kdizon/2P-OPM/CAD/Custom Parts Linked With Drawings/ResGalvoMount_base_plate.stp

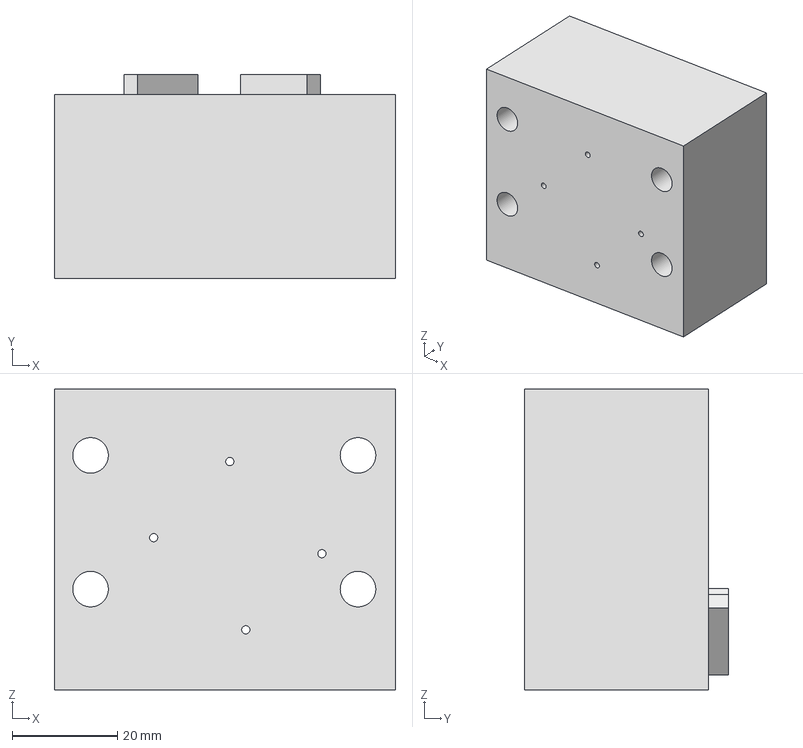
[picture p15: CAD file, 2025-10-08]
CAD/Custom Parts Linked With Drawings/ResGalvoMount_base_plate.stp
64.8 x 38.7 x 57.1 mm
