kdizon/2P-OPM/CAD/Imported Components/Coherent/Sapphire LP Heatsink with dowel pins.STEP

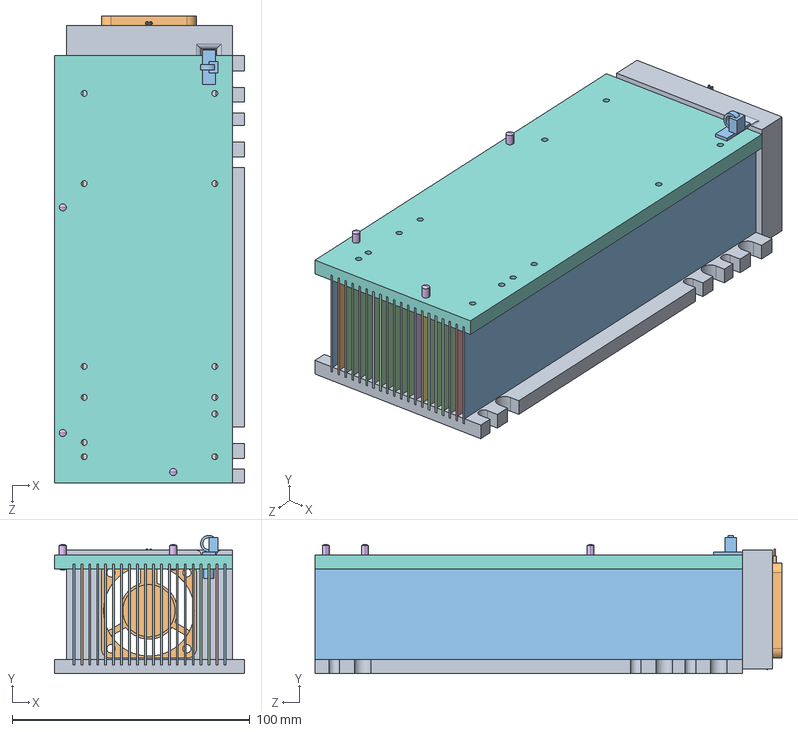
[picture p16: CAD file, 2025-10-09]
CAD/Imported Components/Coherent/Sapphire LP Heatsink with dowel pins.STEP
80.0 x 58.2 x 196.5 mm
