kdizon/2P-OPM/CAD/Imported Components/Edmund/EO_85678.step

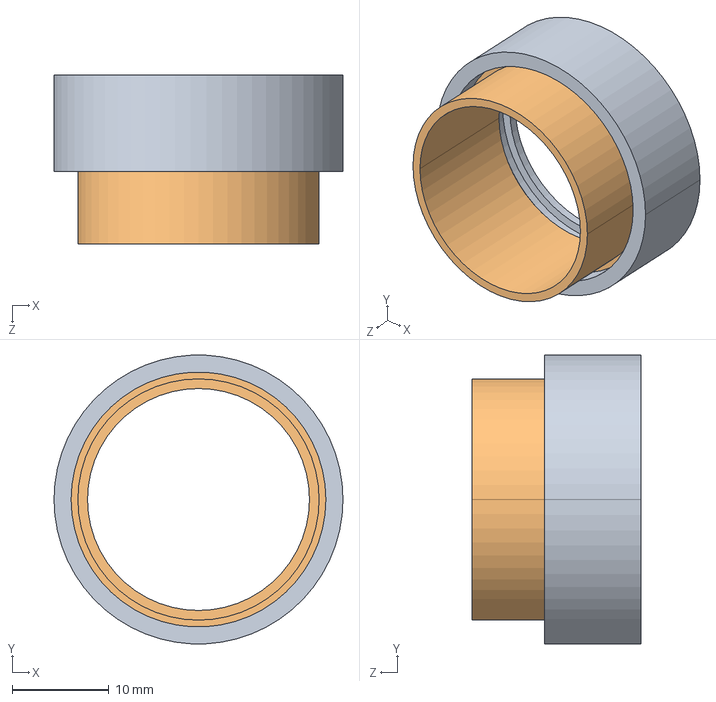
[picture p17: CAD file, 2025-10-09]
CAD/Imported Components/Edmund/EO_85678.step
30.0 x 29.9 x 17.5 mm
