kdizon/2P-OPM/CAD/Imported Components/Newport/Newport-SA2-11.stp

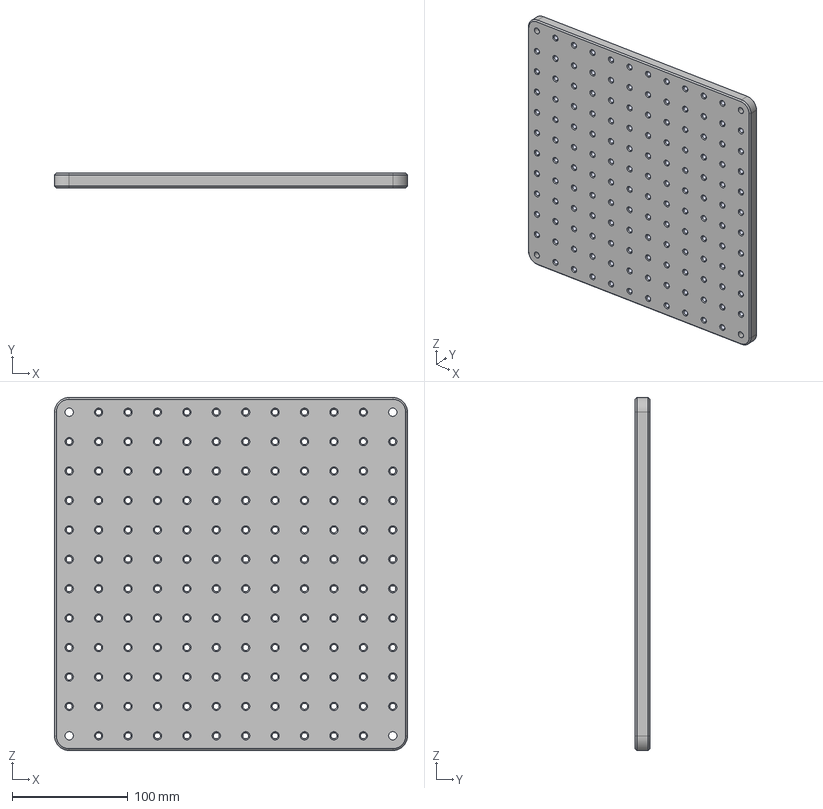
[picture p18: CAD file, 2025-10-09]
CAD/Imported Components/Newport/Newport-SA2-11.stp
304.8 x 12.7 x 304.8 mm
