kdizon/2P-OPM/CAD/Imported Components/PI/P725_1_adapterW0,8.STEP

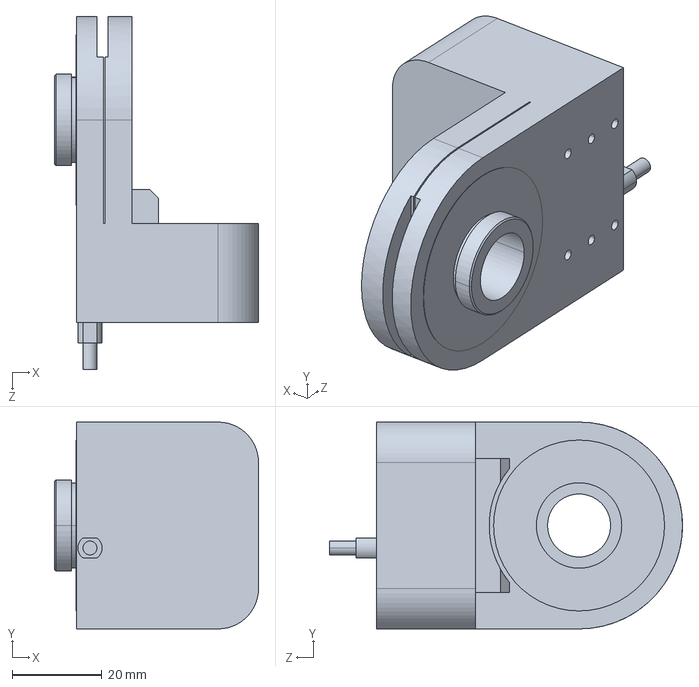
[picture p19: CAD file, 2025-10-09]
CAD/Imported Components/PI/P725_1_adapterW0,8.STEP
45.4 x 46.0 x 78.5 mm
