kdizon/2P-OPM/CAD/1P Laser Combiner/AA Optoelectronc AOTF-nc.sldprt

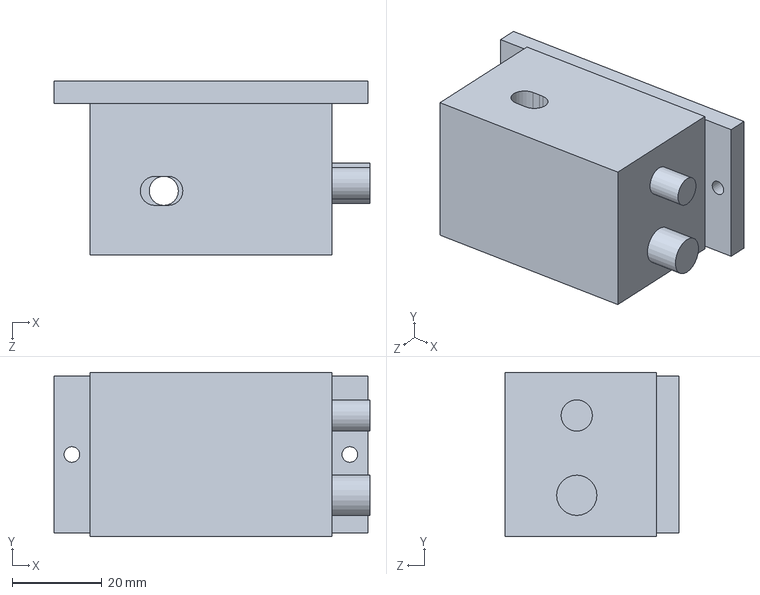
[picture p20: CAD file, 2025-10-08]
CAD/1P Laser Combiner/AA Optoelectronc AOTF-nc.sldprt
70.5 x 36.6 x 38.8 mm
