kdizon/2P-OPM/CAD/Custom Parts Linked With Drawings/xgalvo_to_base_clamp.stp

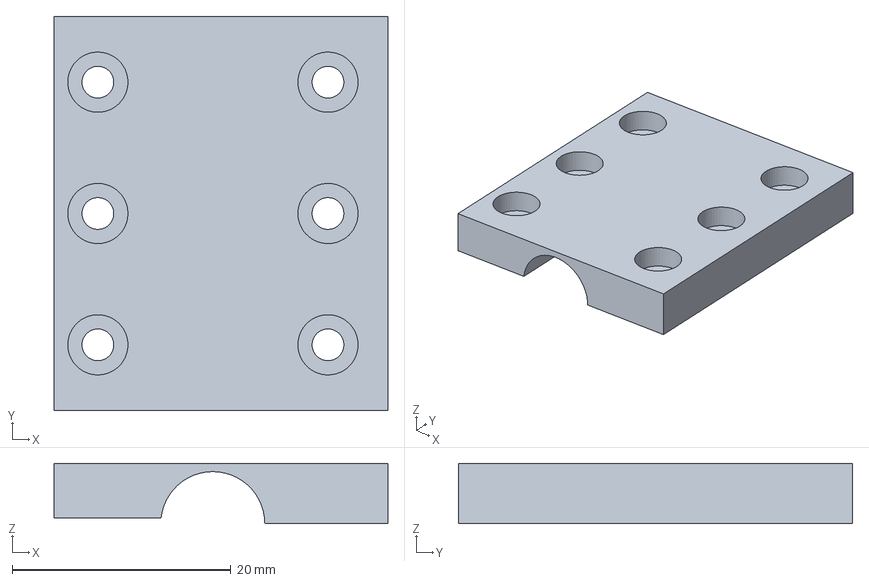
[picture p21: CAD file, 2025-10-08]
CAD/Custom Parts Linked With Drawings/xgalvo_to_base_clamp.stp
30.5 x 36.0 x 5.50 mm
