kdizon/2P-OPM/CAD/Imported Components/Edmund/EO_49287.stp

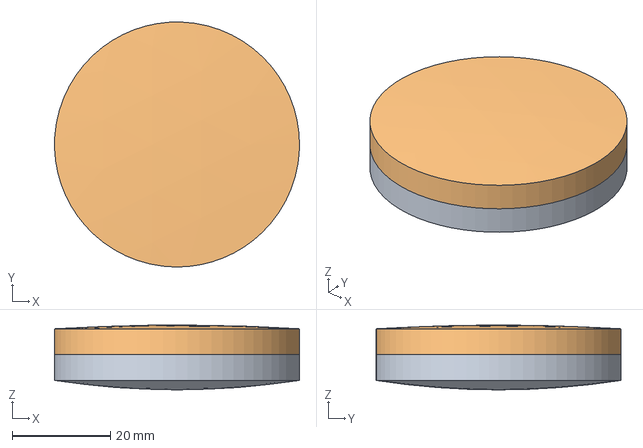
[picture p22: CAD file, 2025-10-09]
CAD/Imported Components/Edmund/EO_49287.stp
50.0 x 50.0 x 13.2 mm
