kdizon/2P-OPM/CAD/Imported Components/Newport/Newport-SA2-12.stp

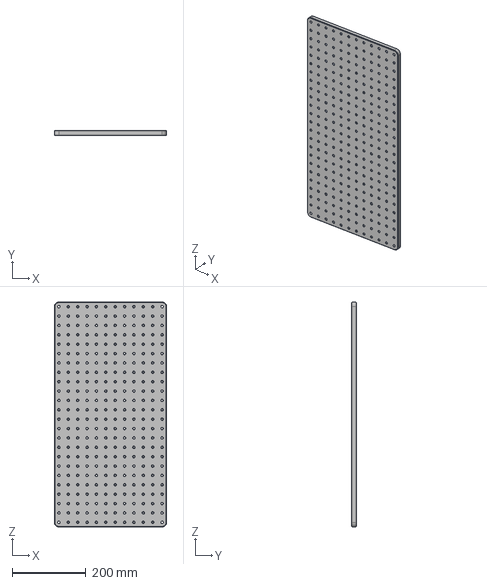
[picture p23: CAD file, 2025-10-09]
CAD/Imported Components/Newport/Newport-SA2-12.stp
304.8 x 12.7 x 609.6 mm
