kdizon/2P-OPM/CAD/Imported Components/PI/P-725.1CX+2CX.STEP

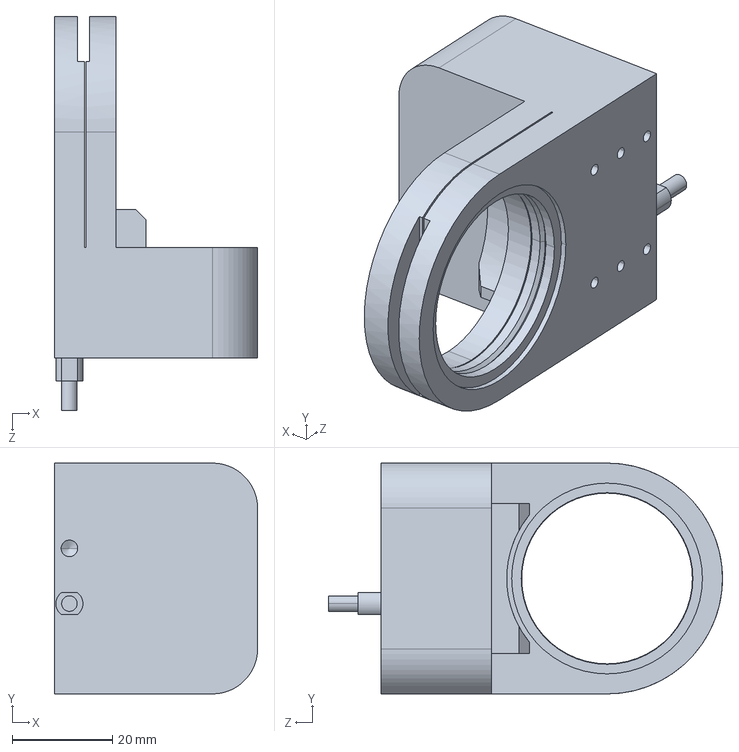
[picture p24: CAD file, 2025-10-09]
CAD/Imported Components/PI/P-725.1CX+2CX.STEP
40.5 x 46.0 x 78.5 mm
