kdizon/2P-OPM/CAD/1P Laser Combiner/Semrock LM01-503-25 LaserMUX dichroic beamsplitter.sldprt

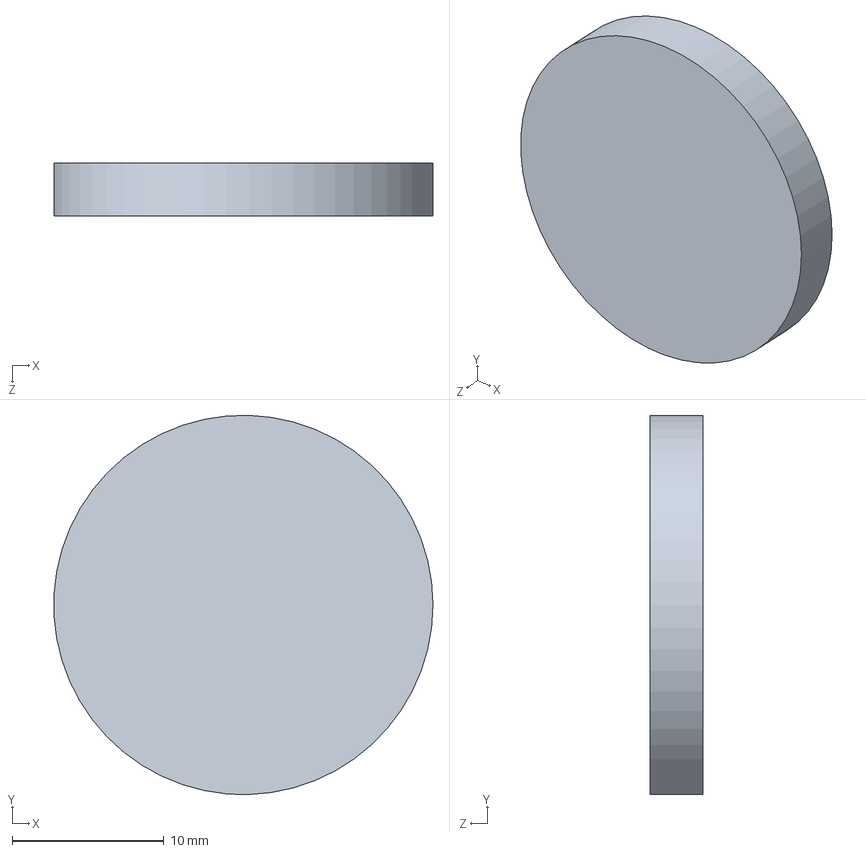
[picture p25: CAD file, 2025-10-08]
CAD/1P Laser Combiner/Semrock LM01-503-25 LaserMUX dichroic beamsplitter.sldprt
25.0 x 25.0 x 3.50 mm
