kdizon/2P-OPM/CAD/Custom Parts Linked With Drawings/ResGalvoMount_wobble.stp

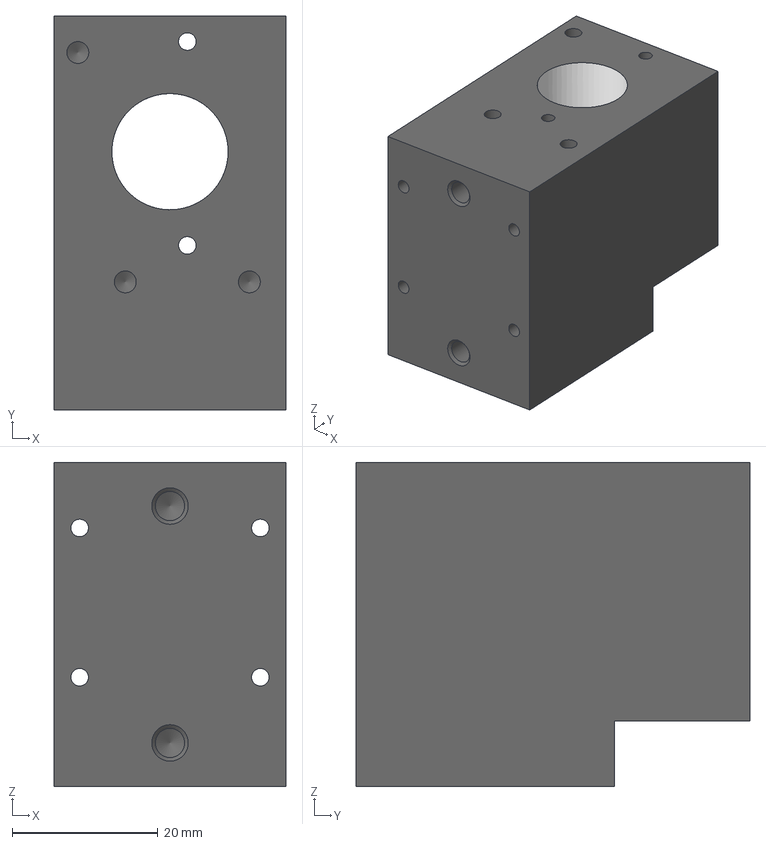
[picture p26: CAD file, 2025-10-08]
CAD/Custom Parts Linked With Drawings/ResGalvoMount_wobble.stp
31.8 x 54.0 x 44.5 mm
