kdizon/2P-OPM/CAD/Imported Components/Edmund/EO_85547.step

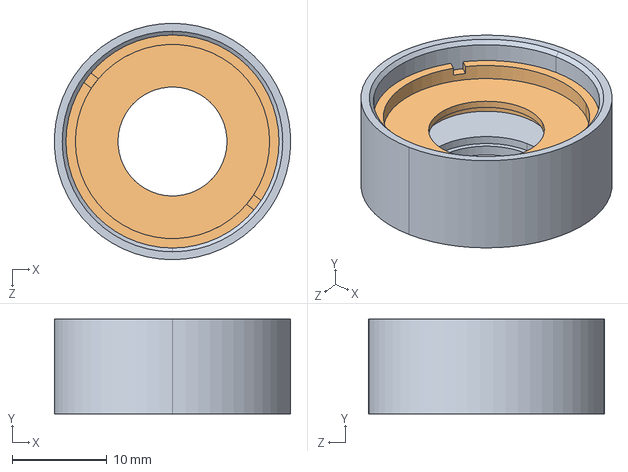
[picture p27: CAD file, 2025-10-09]
CAD/Imported Components/Edmund/EO_85547.step
24.9 x 10.0 x 25.0 mm
