kdizon/2P-OPM/CAD/Imported Components/Newport/Newport-RS4000-48-8.stp

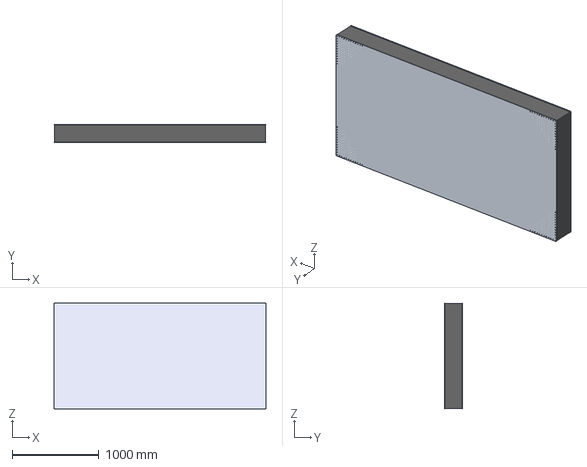
[picture p28: CAD file, 2025-10-09]
CAD/Imported Components/Newport/Newport-RS4000-48-8.stp
2438.4 x 203.2 x 1219.2 mm
