kdizon/2P-OPM/CAD/Imported Components/PI/P-725.2SL.STEP

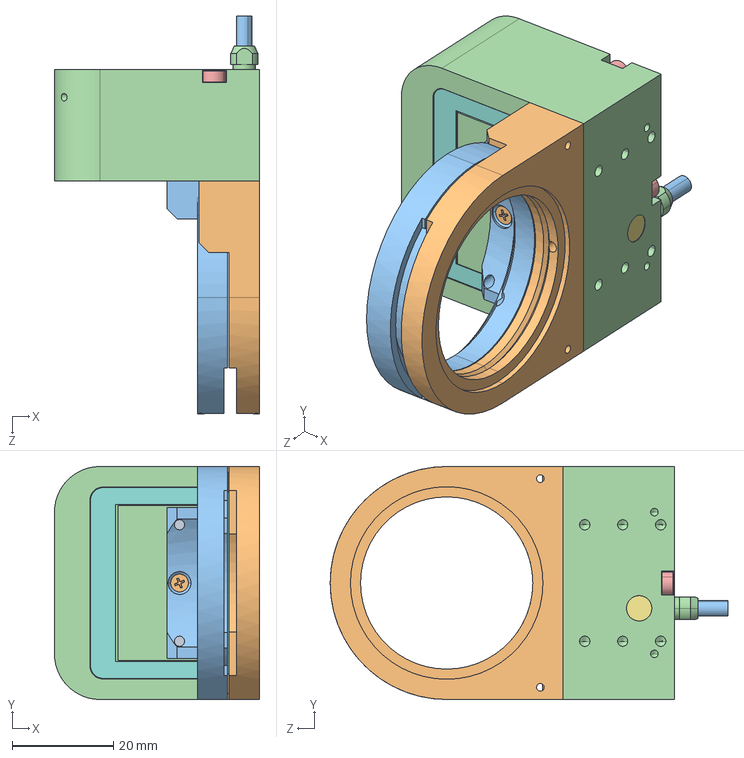
[picture p29: CAD file, 2025-10-09]
CAD/Imported Components/PI/P-725.2SL.STEP
40.5 x 46.0 x 78.5 mm
