kdizon/2P-OPM/CAD/1P Laser Combiner/EO_87371.step

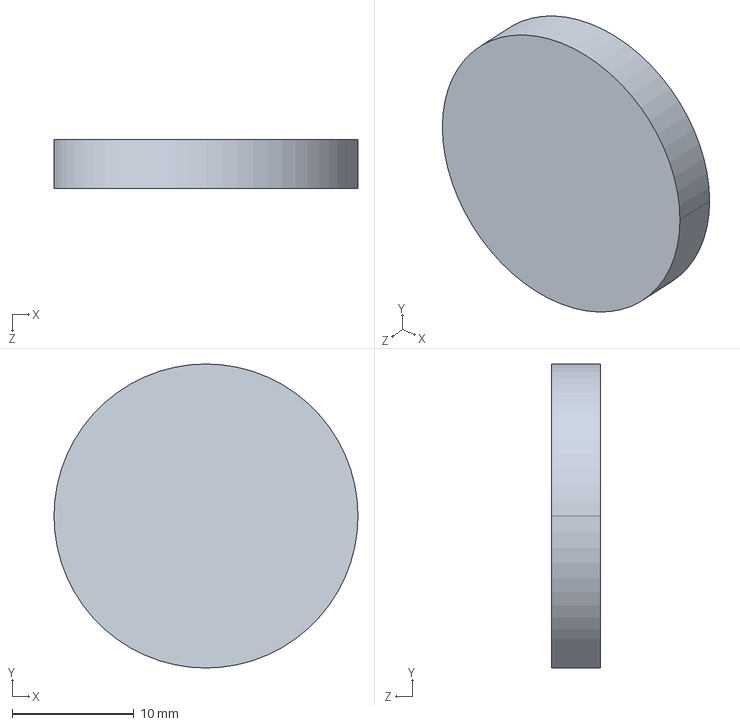
[picture p30: CAD file, 2025-10-08]
CAD/1P Laser Combiner/EO_87371.step
25.0 x 25.0 x 4.00 mm
