kdizon/2P-OPM/CAD/Custom Parts Linked With Drawings/xgalvo_to_newport_stage.stp

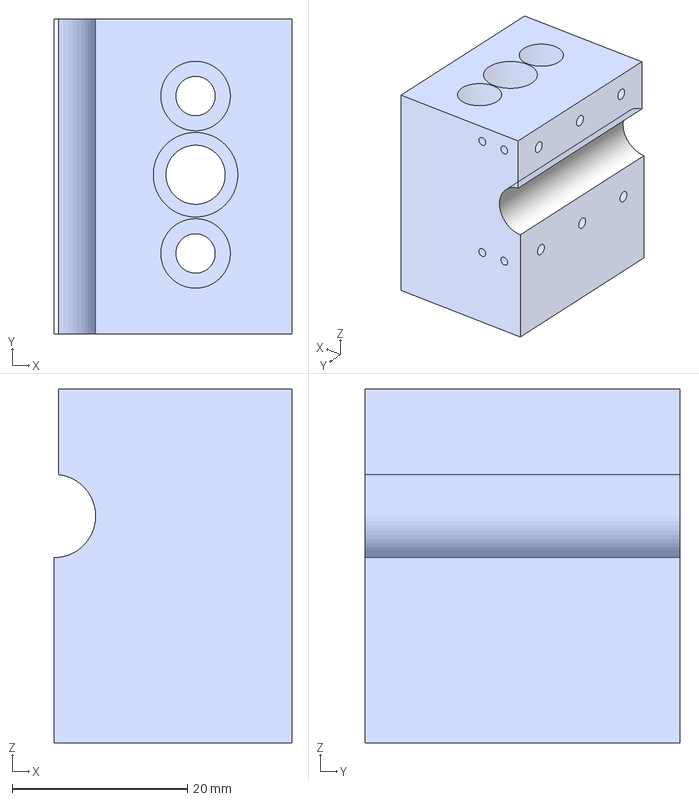
[picture p31: CAD file, 2025-10-08]
CAD/Custom Parts Linked With Drawings/xgalvo_to_newport_stage.stp
27.1 x 36.0 x 40.4 mm
