kdizon/2P-OPM/CAD/Imported Components/Edmund/EO_49304.stp

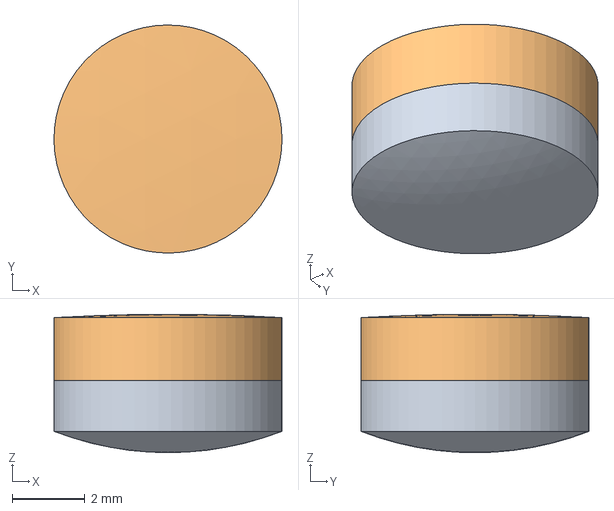
[picture p32: CAD file, 2025-10-09]
CAD/Imported Components/Edmund/EO_49304.stp
6.25 x 6.25 x 3.80 mm
