kdizon/2P-OPM/CAD/Imported Components/Newport/Newport-SM-13.stp

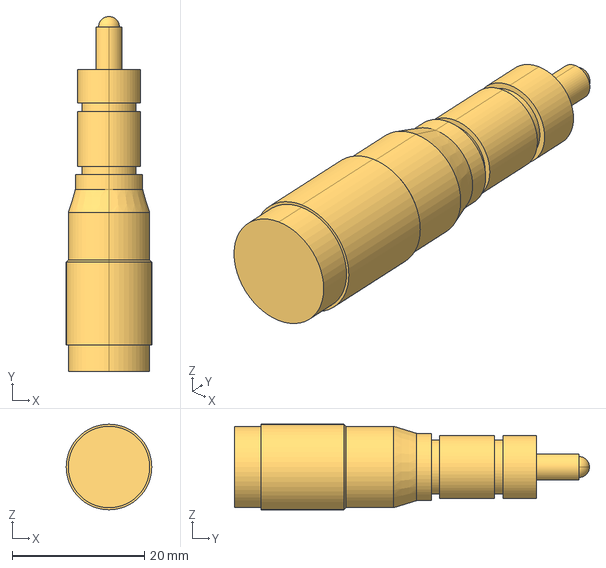
[picture p33: CAD file, 2025-10-09]
CAD/Imported Components/Newport/Newport-SM-13.stp
13.0 x 53.7 x 13.0 mm
