kdizon/2P-OPM/CAD/Custom Parts Linked With Drawings/20-1531-001_ResGalvoClamp.stp

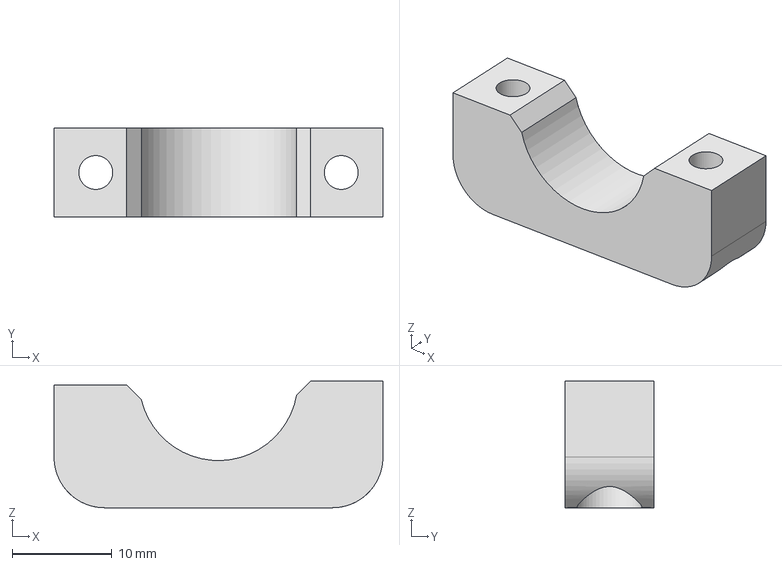
[picture p34: CAD file, 2025-10-08]
CAD/Custom Parts Linked With Drawings/20-1531-001_ResGalvoClamp.stp
33.0 x 8.89 x 12.7 mm
