kdizon/2P-OPM/CAD/Imported Components/Edmund/EO_49392.stp

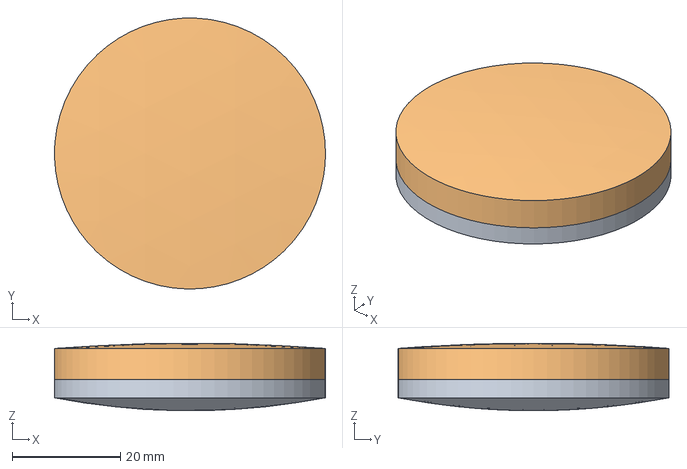
[picture p35: CAD file, 2025-10-09]
CAD/Imported Components/Edmund/EO_49392.stp
50.0 x 50.0 x 12.4 mm
