kdizon/2P-OPM/CAD/Imported Components/Newport/Newport-PRL-36.stp

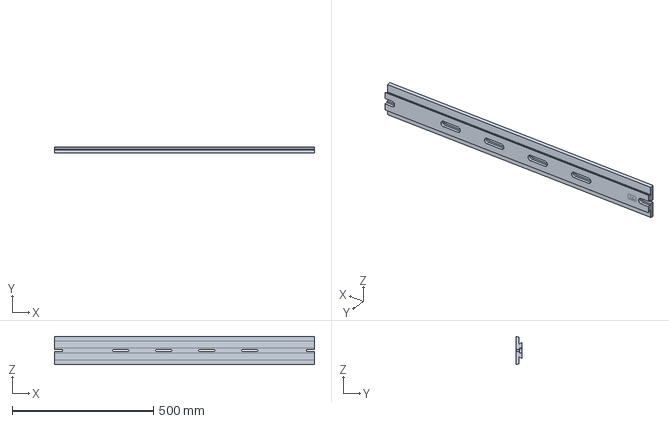
[picture p36: CAD file, 2025-10-09]
CAD/Imported Components/Newport/Newport-PRL-36.stp
921.5 x 21.1 x 99.3 mm
