kdizon/2P-OPM/CAD/Imported Components/Edmund/EO_right-angle-bracket_55378.step

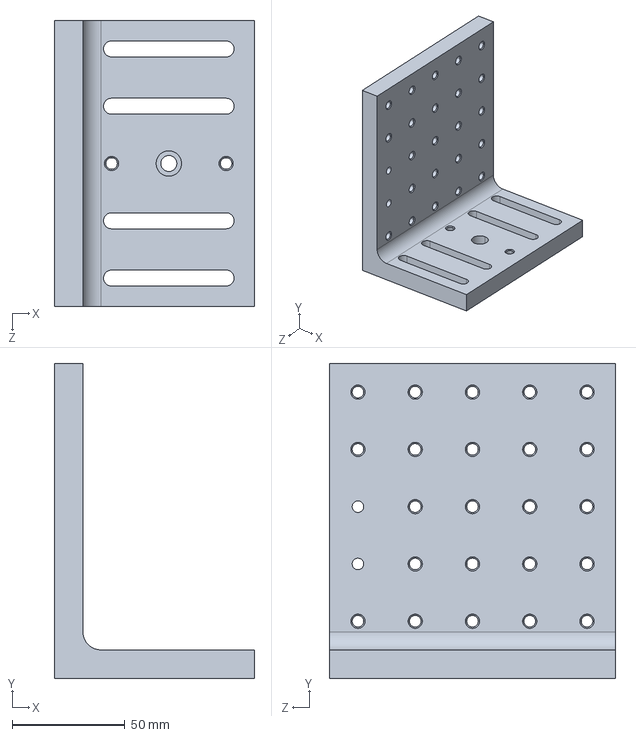
[picture p37: CAD file, 2025-10-09]
CAD/Imported Components/Edmund/EO_right-angle-bracket_55378.step
88.9 x 139.7 x 127.0 mm
