kdizon/2P-OPM/CAD/Imported Components/Newport/Newport-SM-25.stp

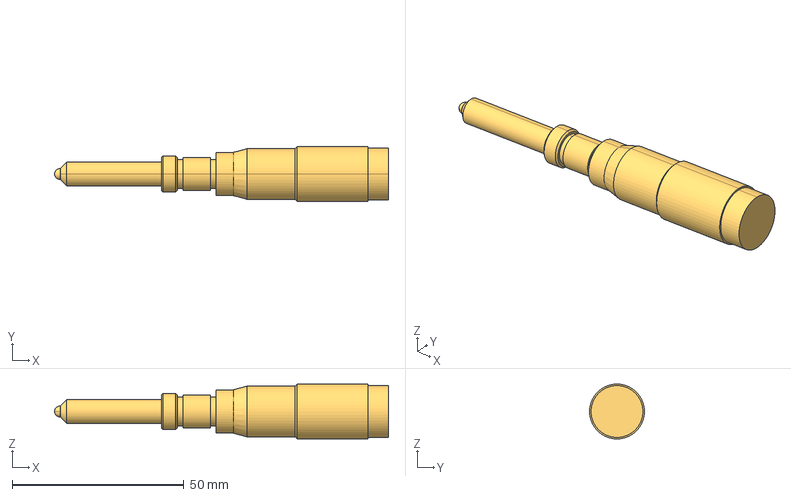
[picture p38: CAD file, 2025-10-09]
CAD/Imported Components/Newport/Newport-SM-25.stp
97.3 x 16.0 x 16.0 mm
