kdizon/2P-OPM/CAD/Imported Components/Edmund/EO_88196.STEP

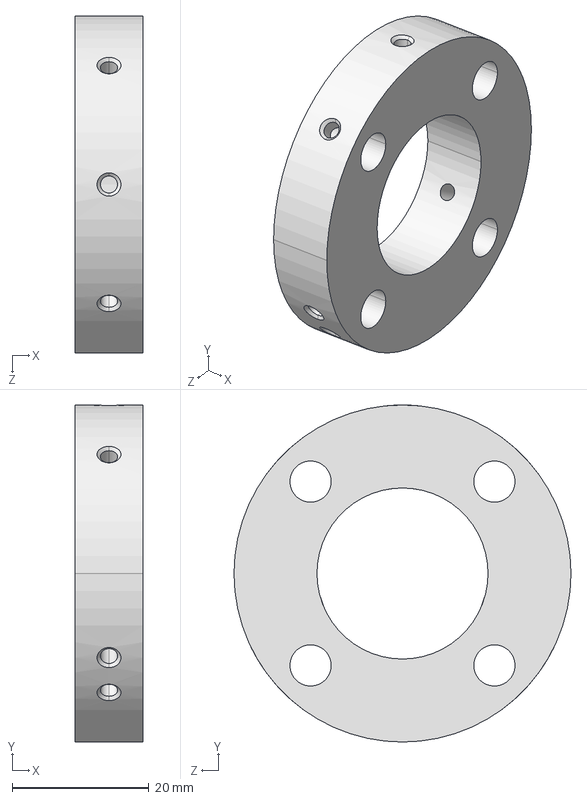
[picture p39: CAD file, 2025-10-09]
CAD/Imported Components/Edmund/EO_88196.STEP
10.0 x 49.2 x 49.2 mm
