kdizon/2P-OPM/CAD/Imported Components/Newport/Newport-TD-23.stp

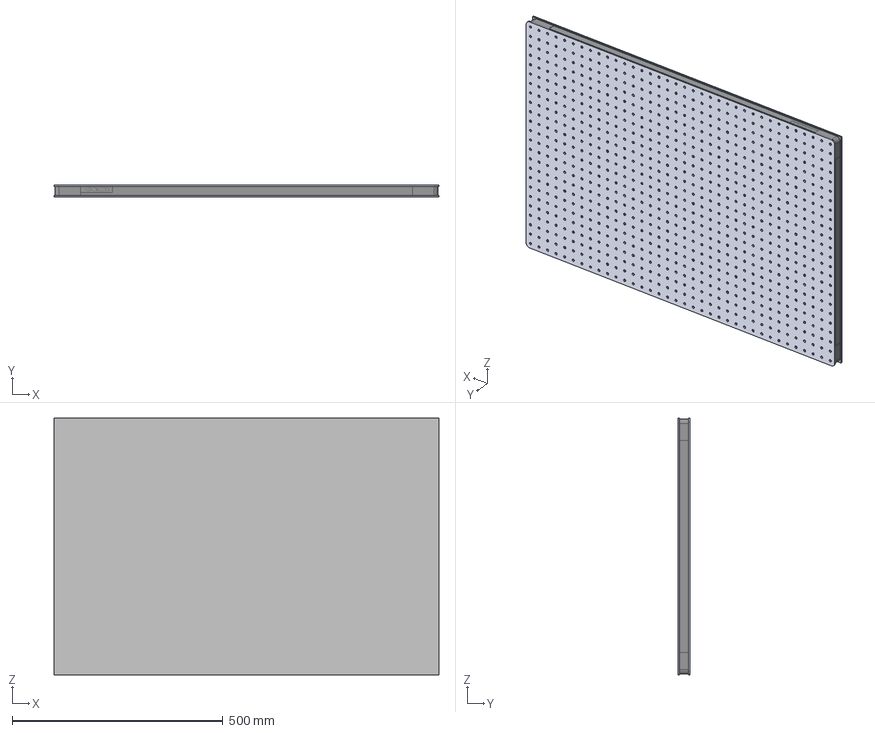
[picture p40: CAD file, 2025-10-09]
CAD/Imported Components/Newport/Newport-TD-23.stp
914.4 x 27.4 x 609.6 mm
