kdizon/2P-OPM/CAD/1P Laser Combiner/mirror translation stage adapter - 2P-OPM.stp

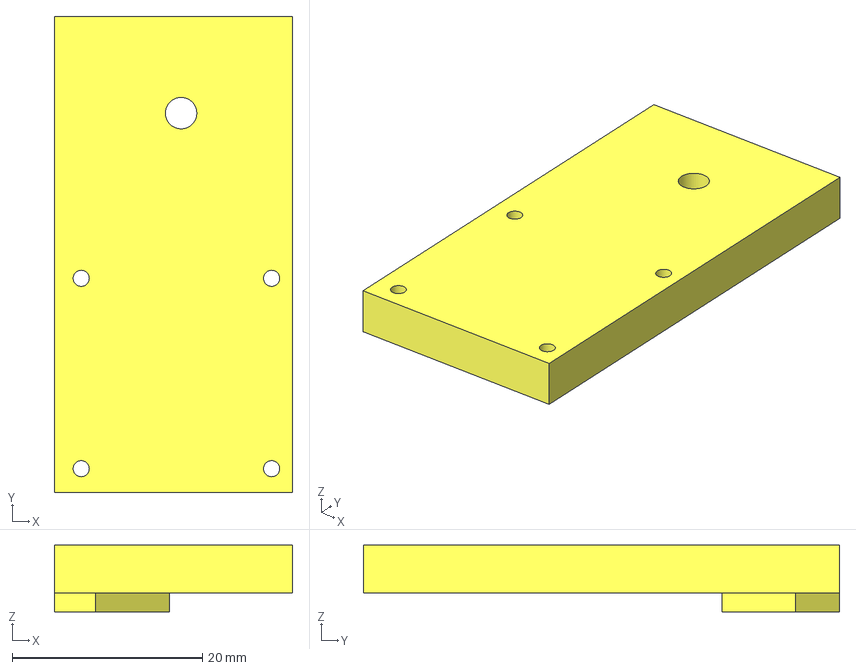
[picture p41: CAD file, 2025-10-08]
CAD/1P Laser Combiner/mirror translation stage adapter - 2P-OPM.stp
25.0 x 50.0 x 7.00 mm
