kdizon/2P-OPM/CAD/Imported Components/Edmund/EO_12.5mmDia_90mmFL_49332.stp

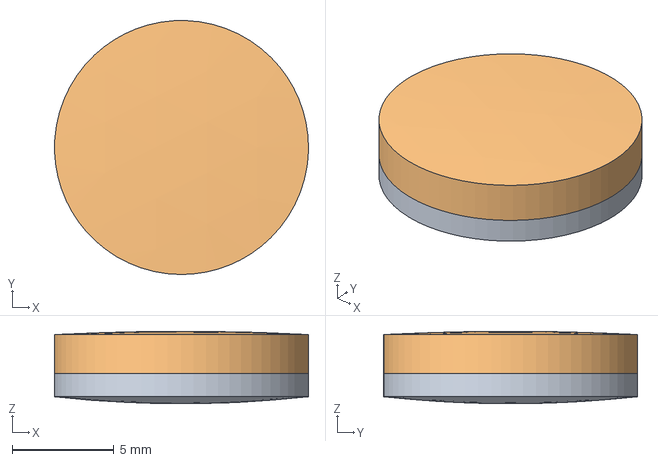
[picture p42: CAD file, 2025-10-09]
CAD/Imported Components/Edmund/EO_12.5mmDia_90mmFL_49332.stp
12.5 x 12.5 x 3.57 mm
