kdizon/2P-OPM/CAD/Imported Components/Newport/Newport-PRC-1.stp

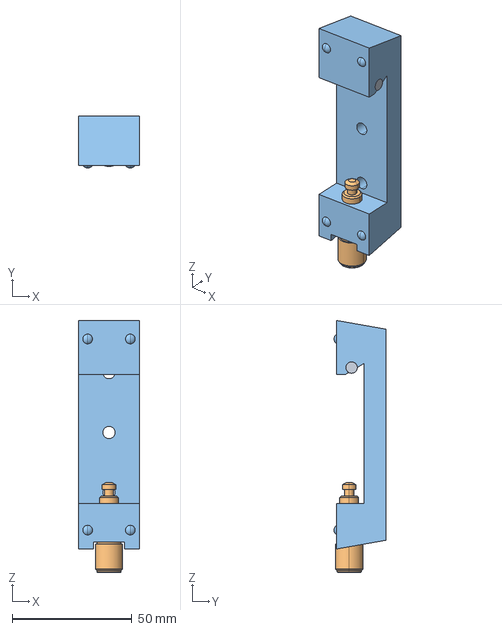
[picture p43: CAD file, 2025-10-09]
CAD/Imported Components/Newport/Newport-PRC-1.stp
25.4 x 21.7 x 105.2 mm
