kdizon/2P-OPM/CAD/1P Laser Combiner/baseblock for AOTF.stp

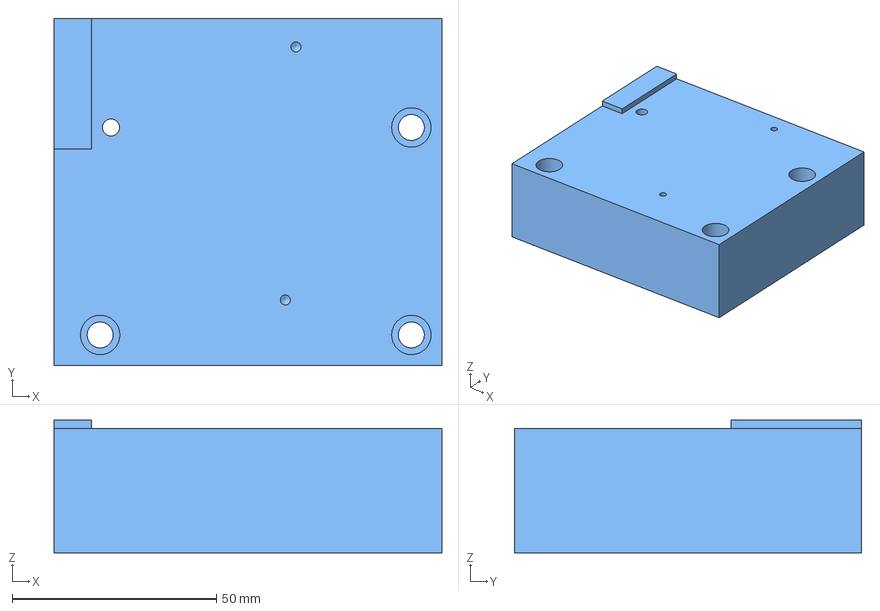
[picture p44: CAD file, 2025-10-08]
CAD/1P Laser Combiner/baseblock for AOTF.stp
95.0 x 85.0 x 32.5 mm
