kdizon/2P-OPM/CAD/Imported Components/Edmund/EO_84747.step

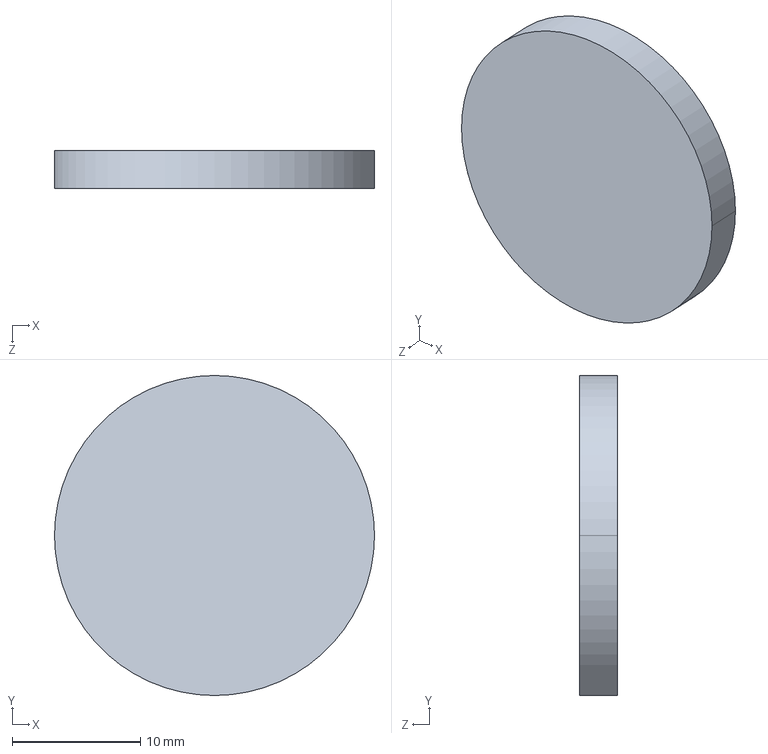
[picture p45: CAD file, 2025-10-09]
CAD/Imported Components/Edmund/EO_84747.step
25.0 x 25.0 x 3.00 mm
