kdizon/2P-OPM/CAD/Imported Components/Newport/Newport-B-2B.stp

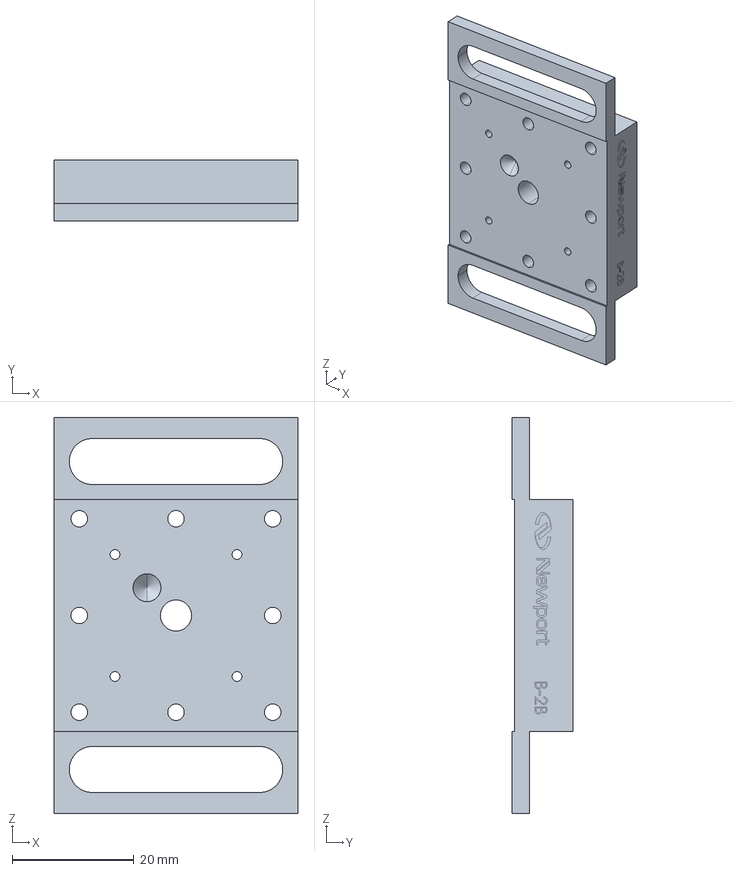
[picture p46: CAD file, 2025-10-09]
CAD/Imported Components/Newport/Newport-B-2B.stp
40.0 x 10.0 x 65.0 mm
