kdizon/2P-OPM/CAD/Imported Components/Edmund/EO_49288.stp

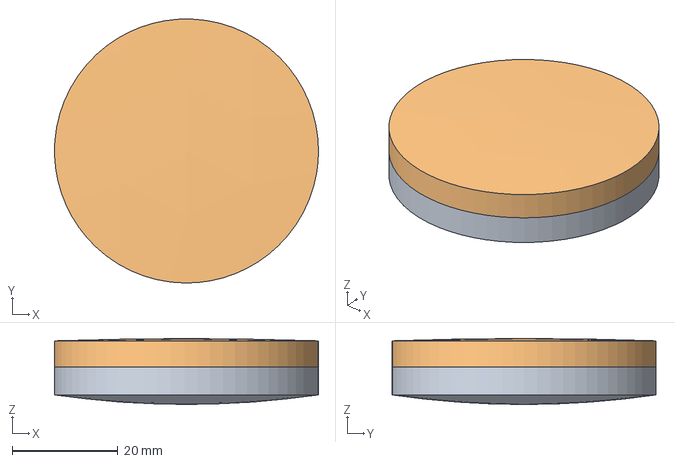
[picture p47: CAD file, 2025-10-09]
CAD/Imported Components/Edmund/EO_49288.stp
50.0 x 50.0 x 12.5 mm
