kdizon/2P-OPM/CAD/Imported Components/Newport/Newport-9884.stp

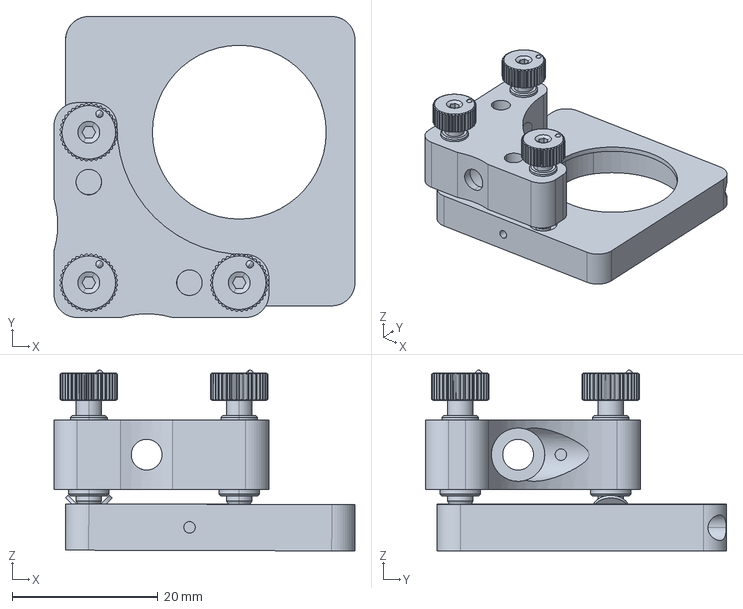
[picture p48: CAD file, 2025-10-09]
CAD/Imported Components/Newport/Newport-9884.stp
41.3 x 41.3 x 24.8 mm
