kdizon/2P-OPM/CAD/1P Laser Combiner/MRA10-E02 right angle prism dielectric coat.sldprt

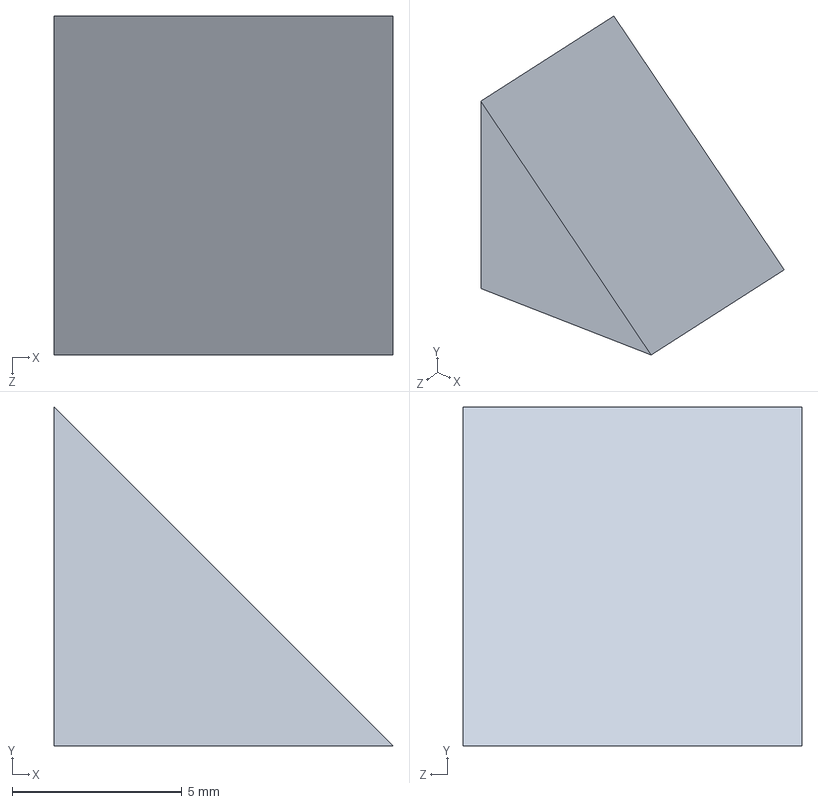
[picture p49: CAD file, 2025-10-08]
CAD/1P Laser Combiner/MRA10-E02 right angle prism dielectric coat.sldprt
10.0 x 10.0 x 10.0 mm
