kdizon/2P-OPM/CAD/Imported Components/Edmund/EO_49364.stp

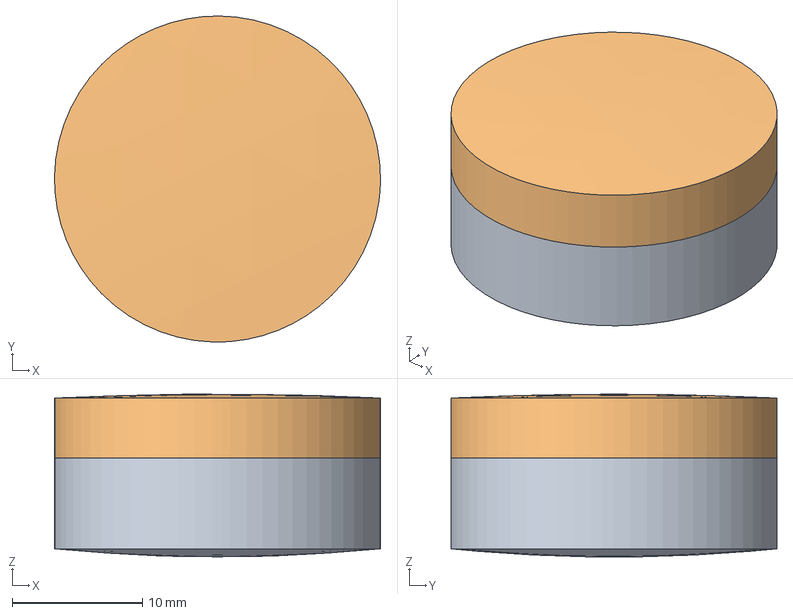
[picture p50: CAD file, 2025-10-09]
CAD/Imported Components/Edmund/EO_49364.stp
25.0 x 25.0 x 12.5 mm
