kdizon/2P-OPM/CAD/Imported Components/Newport/Newport-DS40-X.stp

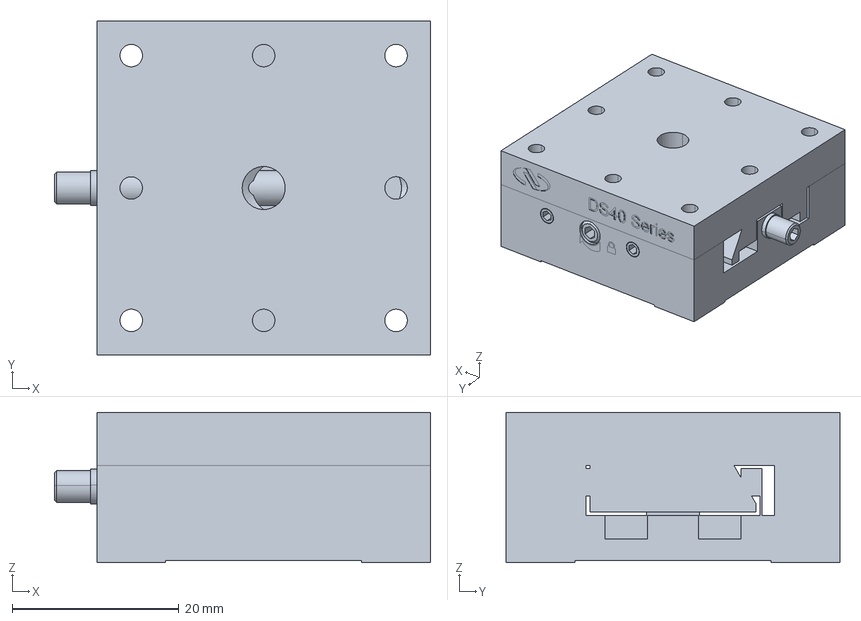
[picture p51: CAD file, 2025-10-09]
CAD/Imported Components/Newport/Newport-DS40-X.stp
45.1 x 40.0 x 18.0 mm
