kdizon/2P-OPM/CAD/Imported Components/Edmund/EO_85536.step

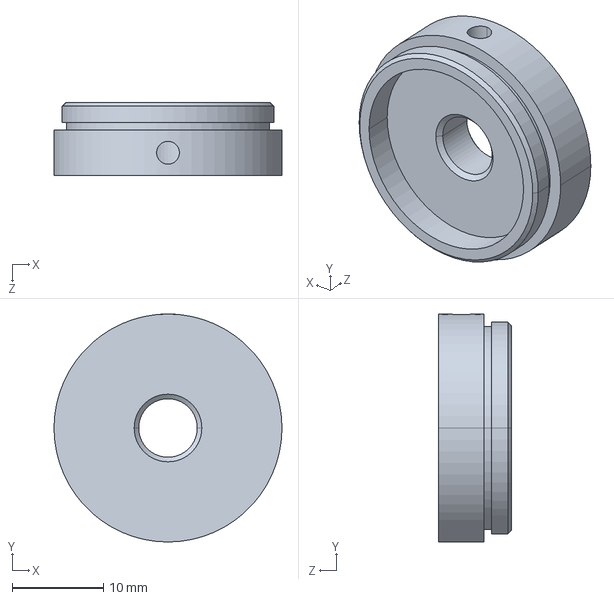
[picture p52: CAD file, 2025-10-09]
CAD/Imported Components/Edmund/EO_85536.step
25.0 x 25.0 x 8.00 mm
