kdizon/2P-OPM/CAD/Imported Components/Newport/Newport-PRL-12.stp

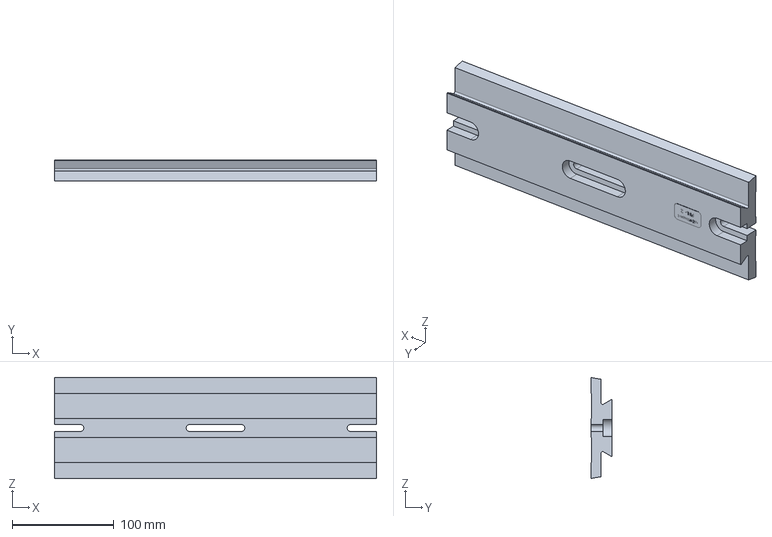
[picture p53: CAD file, 2025-10-09]
CAD/Imported Components/Newport/Newport-PRL-12.stp
316.5 x 21.1 x 99.3 mm
