kdizon/2P-OPM/CAD/Imported Components/Edmund/EO_47661.stp

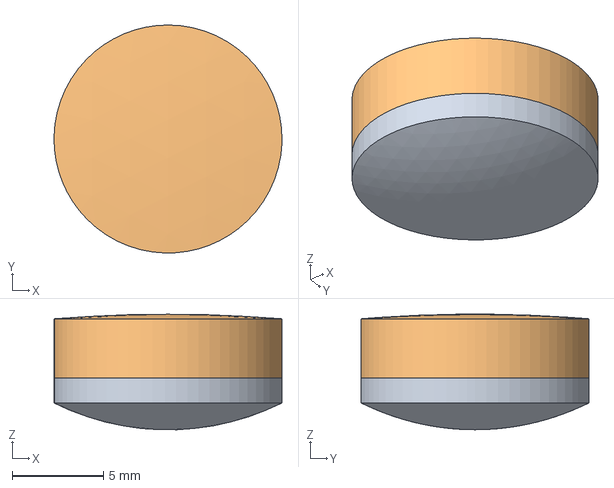
[picture p54: CAD file, 2025-10-09]
CAD/Imported Components/Edmund/EO_47661.stp
12.5 x 12.5 x 6.33 mm
