kdizon/2P-OPM/CAD/Imported Components/Newport/Newport-AJS100-1.stp

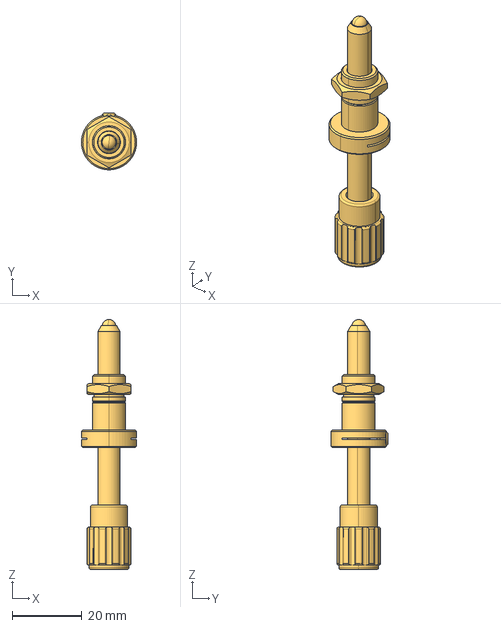
[picture p55: CAD file, 2025-10-09]
CAD/Imported Components/Newport/Newport-AJS100-1.stp
15.9 x 16.3 x 71.9 mm
