kdizon/2P-OPM/CAD/Imported Components/Edmund/EO_slotted_right-angle-bracket_58181.step

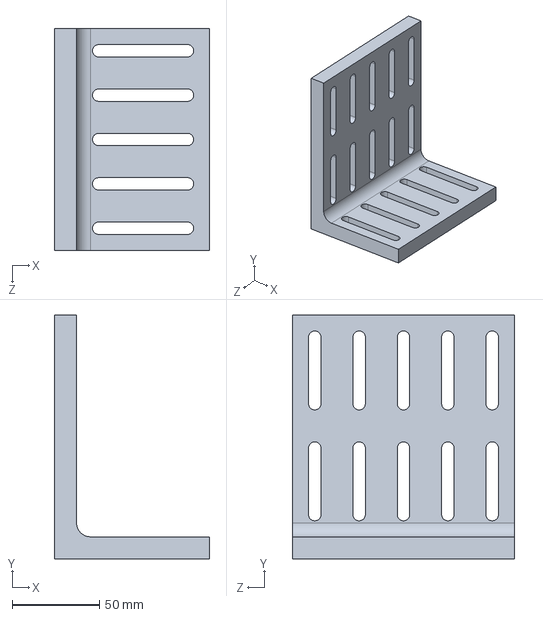
[picture p56: CAD file, 2025-10-09]
CAD/Imported Components/Edmund/EO_slotted_right-angle-bracket_58181.step
88.9 x 139.7 x 127.0 mm
