kdizon/2P-OPM/CAD/Imported Components/Newport/Newport-9066-XY.stp

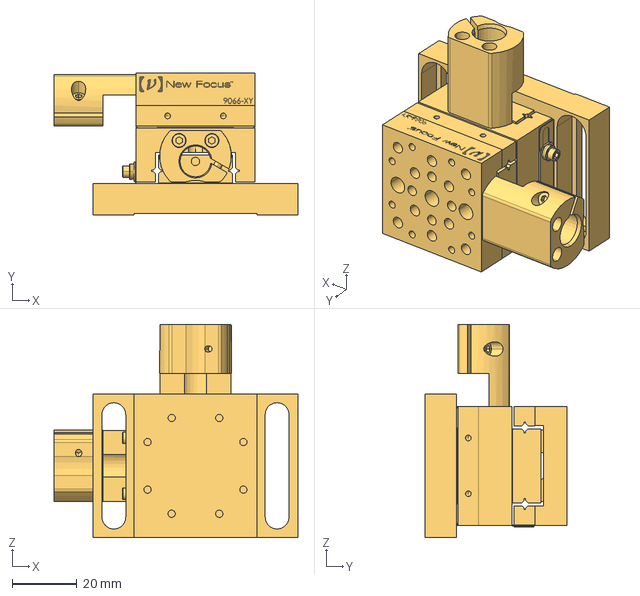
[picture p57: CAD file, 2025-10-09]
CAD/Imported Components/Newport/Newport-9066-XY.stp
75.6 x 44.1 x 66.0 mm
