kdizon/2P-OPM/CAD/Imported Components/Newport/Newport-433.stp

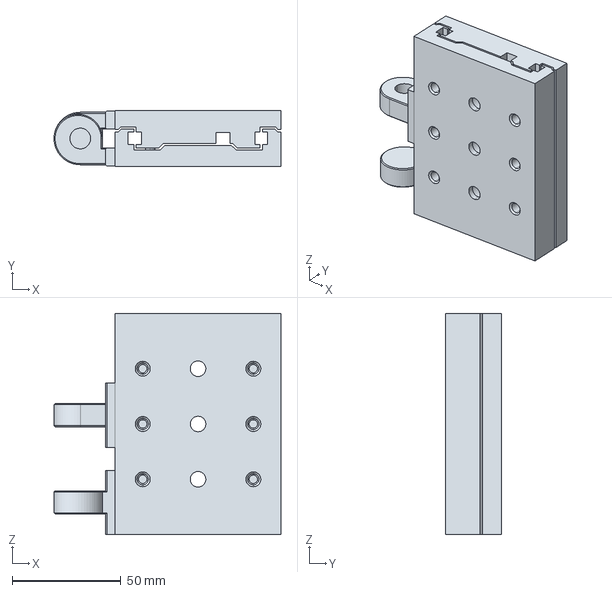
[picture p59: CAD file, 2025-10-09]
CAD/Imported Components/Newport/Newport-433.stp
104.3 x 25.7 x 101.6 mm
