kdizon/2P-OPM/CAD/Imported Components/Edmund/EO_49362.stp

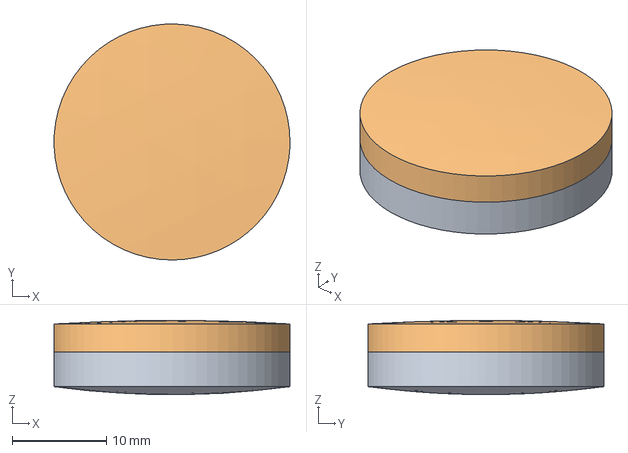
[picture p60: CAD file, 2025-10-09]
CAD/Imported Components/Edmund/EO_49362.stp
25.0 x 25.0 x 7.87 mm
