kdizon/2P-OPM/CAD/Imported Components/Newport/Newport-436.stp

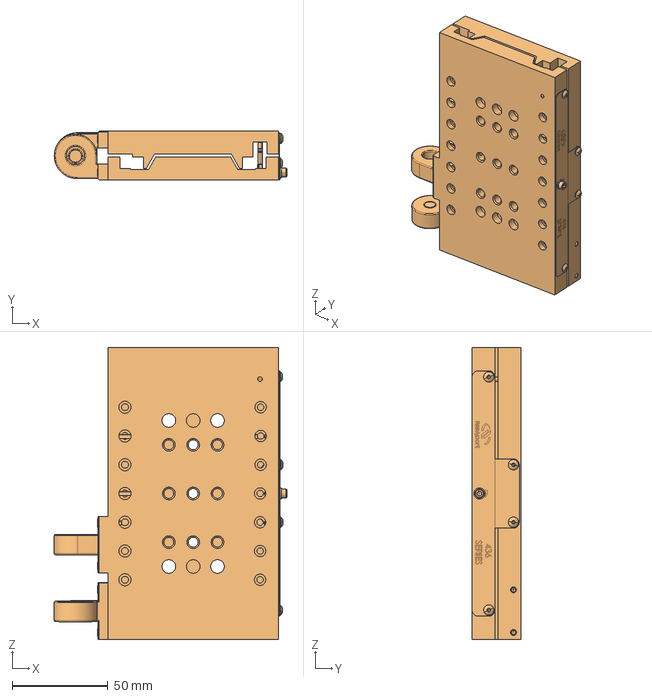
[picture p61: CAD file, 2025-10-09]
CAD/Imported Components/Newport/Newport-436.stp
121.4 x 25.5 x 152.4 mm
