kdizon/2P-OPM/CAD/Imported Components/Edmund/EO_small-slotted_right-angle-bracket_58180.step

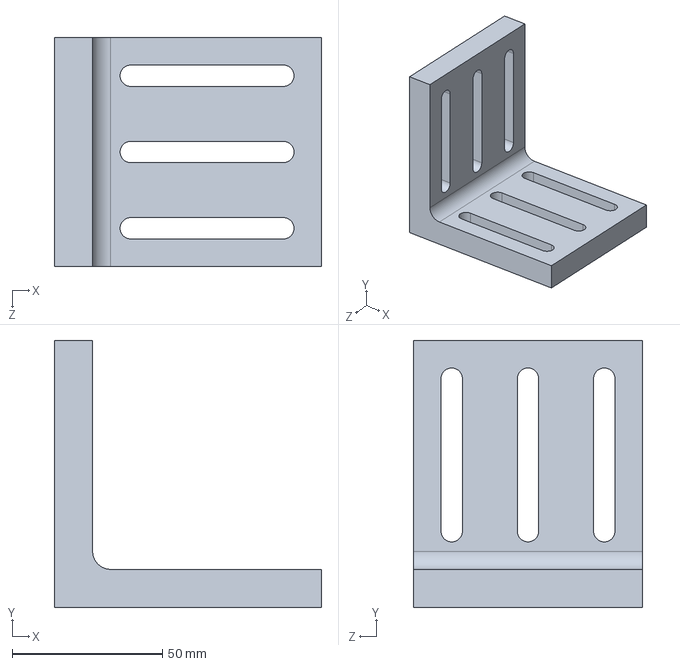
[picture p62: CAD file, 2025-10-09]
CAD/Imported Components/Edmund/EO_small-slotted_right-angle-bracket_58180.step
88.9 x 88.9 x 76.2 mm
