kdizon/2P-OPM/CAD/Imported Components/Newport/Newport-8892-K.stp

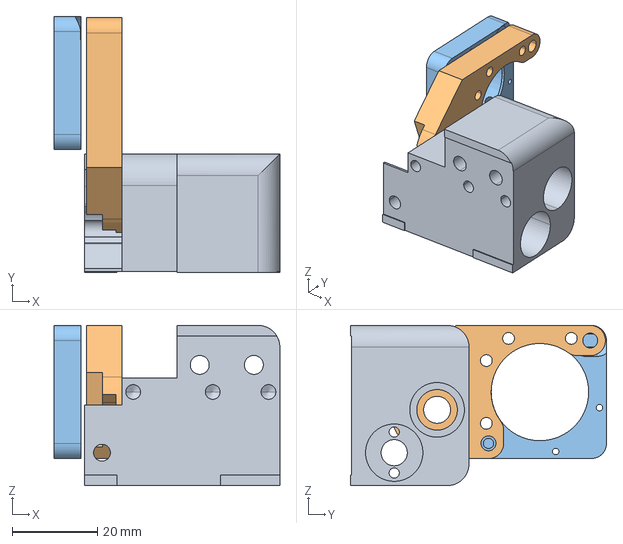
[picture p63: CAD file, 2025-10-09]
CAD/Imported Components/Newport/Newport-8892-K.stp
53.0 x 60.1 x 37.6 mm
