kdizon/2P-OPM/CAD/Imported Components/Edmund/EO_49947.stp

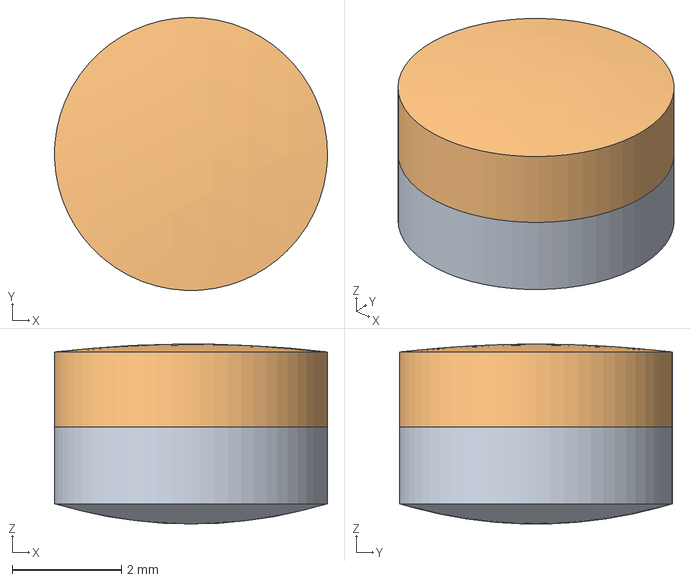
[picture p64: CAD file, 2025-10-09]
CAD/Imported Components/Edmund/EO_49947.stp
5.00 x 5.00 x 3.29 mm
