kdizon/2P-OPM/CAD/Imported Components/Newport/Newport-443.stp

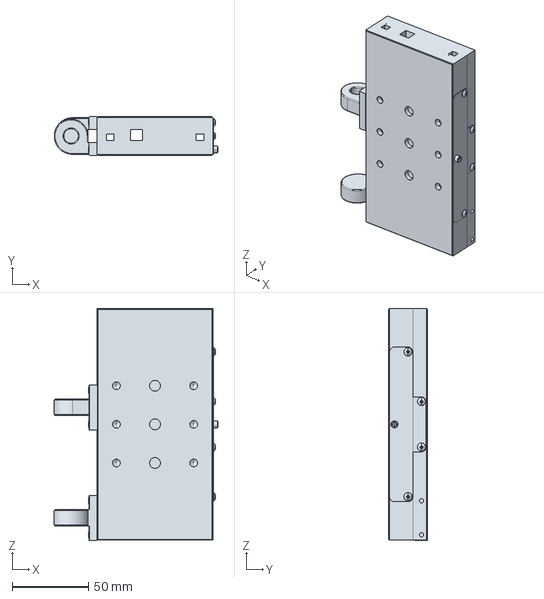
[picture p65: CAD file, 2025-10-09]
CAD/Imported Components/Newport/Newport-443.stp
107.5 x 25.4 x 152.6 mm
