kdizon/2P-OPM/CAD/Imported Components/Newport/Newport-9481.stp

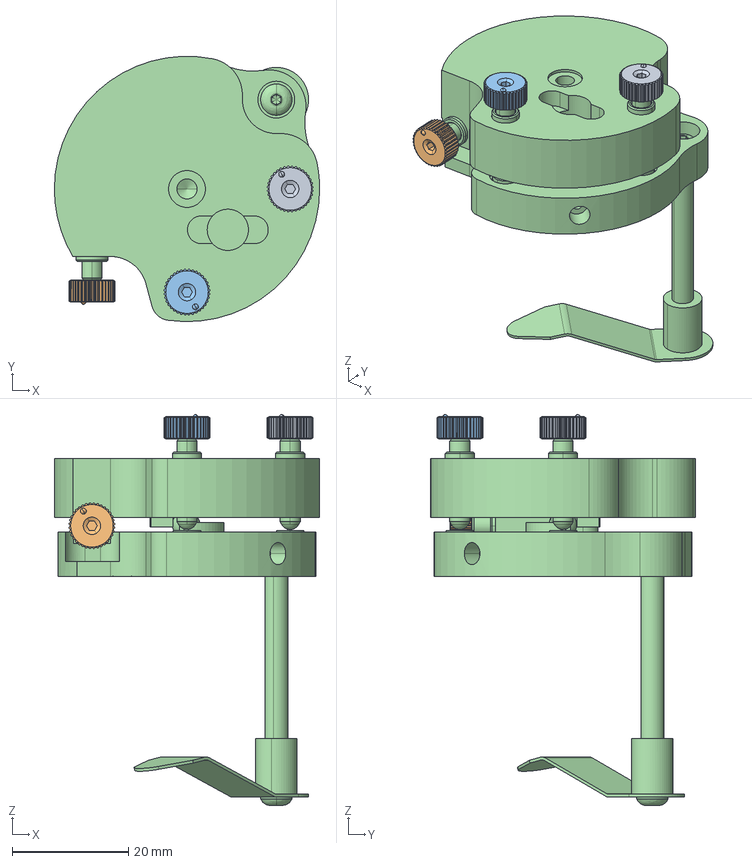
[picture p66: CAD file, 2025-10-09]
CAD/Imported Components/Newport/Newport-9481.stp
45.7 x 45.7 x 67.4 mm
