kdizon/2P-OPM/CAD/Imported Components/Newport/Newport-423.stp

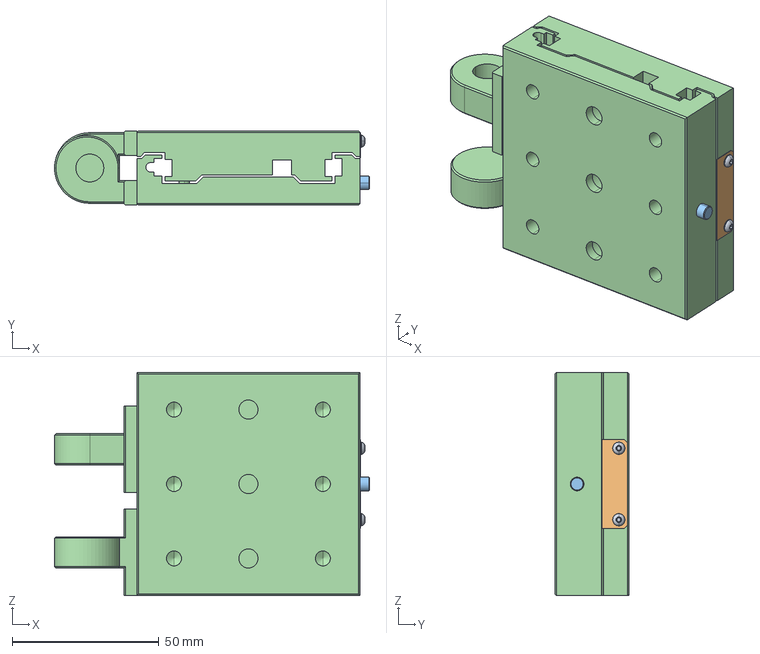
[picture p67: CAD file, 2025-10-09]
CAD/Imported Components/Newport/Newport-423.stp
107.5 x 25.4 x 76.2 mm
